tristanmcooper/courtside/plots/oura_daily_scores.png

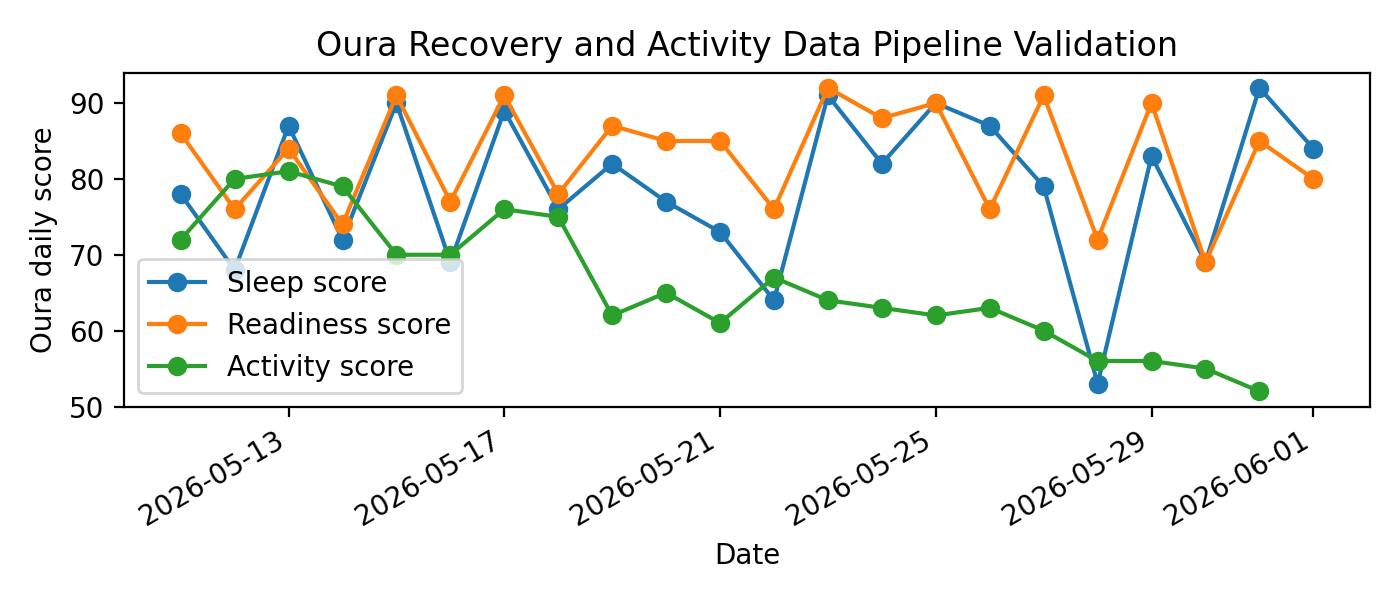
plots/oura_daily_scores.png
