tristanmcooper/courtside/updated app visuals/IMG_5117.PNG

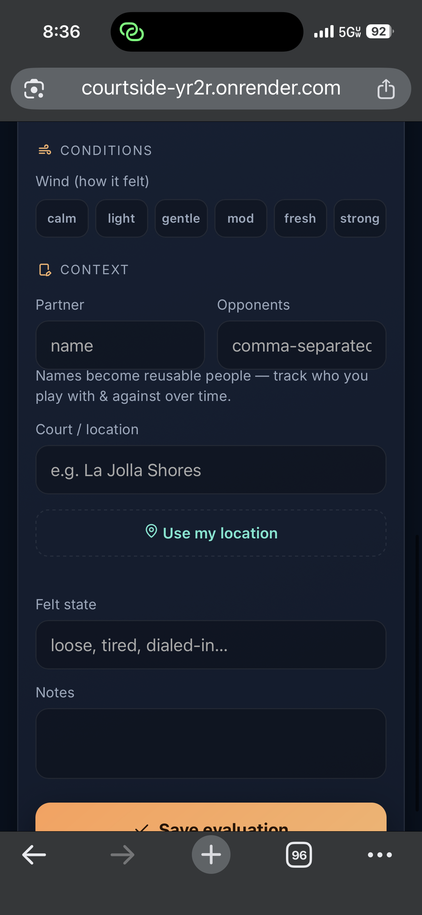
updated app visuals/IMG_5117.PNG
