tristanmcooper/courtside/updated app visuals/IMG_5119.PNG

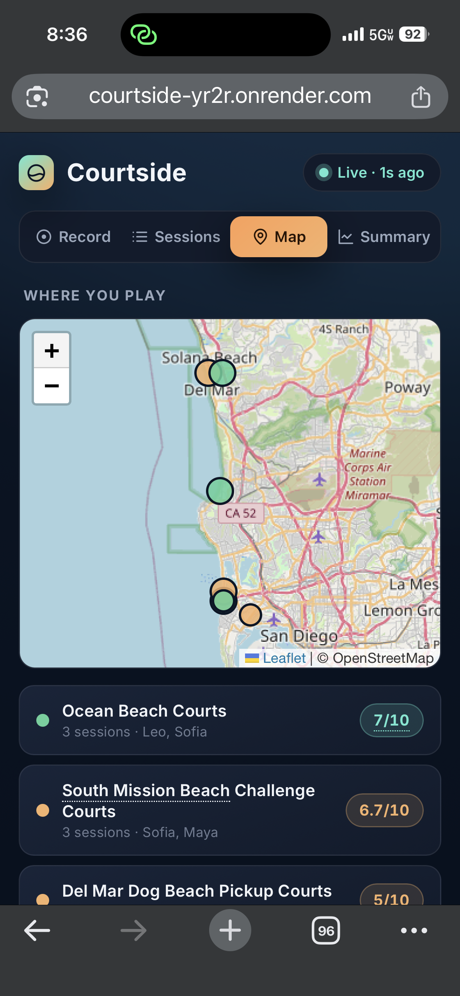
updated app visuals/IMG_5119.PNG
