tristanmcooper/courtside/updated app visuals/IMG_5123.PNG

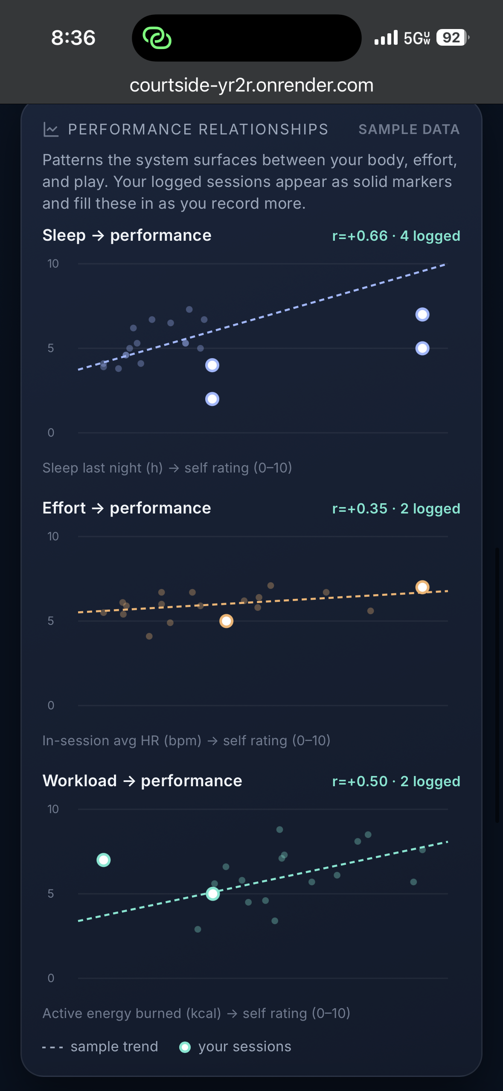
updated app visuals/IMG_5123.PNG
