tristanmcooper/courtside/updated app visuals/IMG_5125.PNG

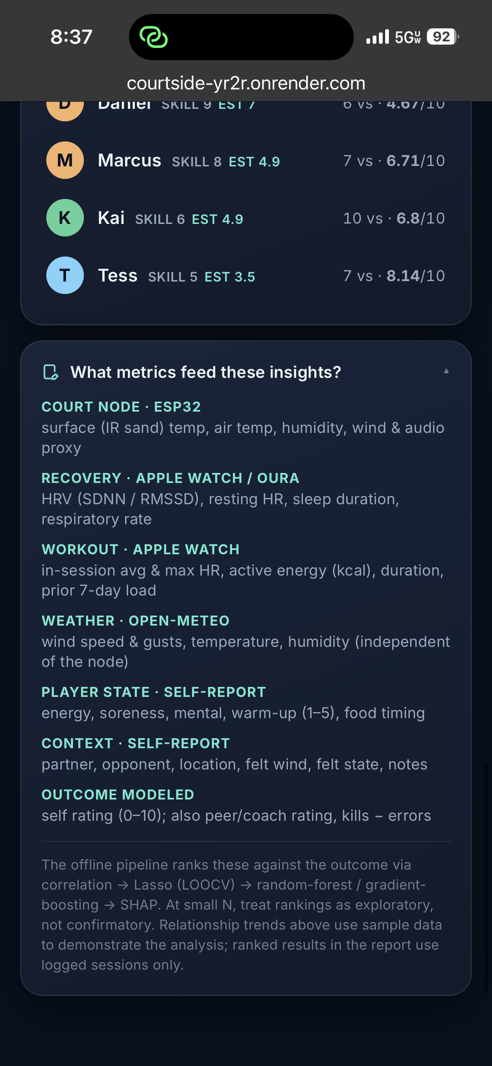
updated app visuals/IMG_5125.PNG
