tristanmcooper/courtside/visuals_for_writeup/IMG_5112.PNG

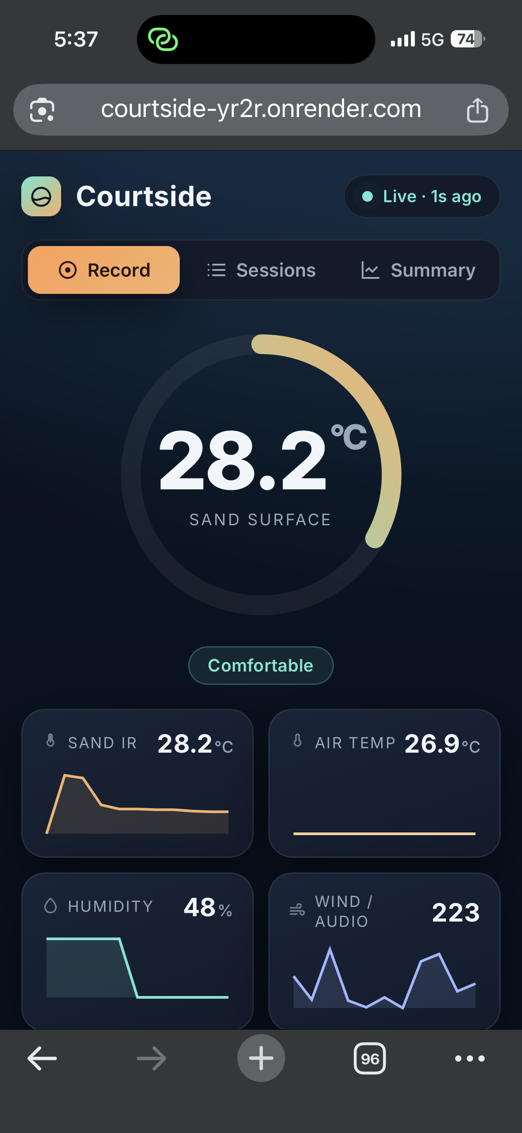
visuals_for_writeup/IMG_5112.PNG
