tristanmcooper/courtside/visuals_for_writeup/IMG_5113.PNG

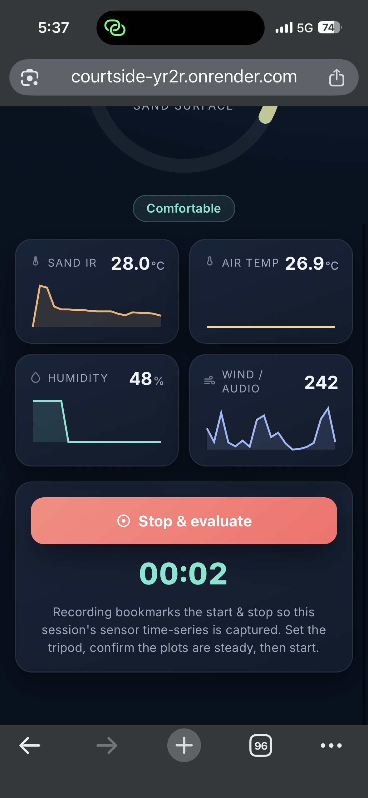
visuals_for_writeup/IMG_5113.PNG
