tristanmcooper/courtside/visuals_for_writeup/IMG_5114.PNG

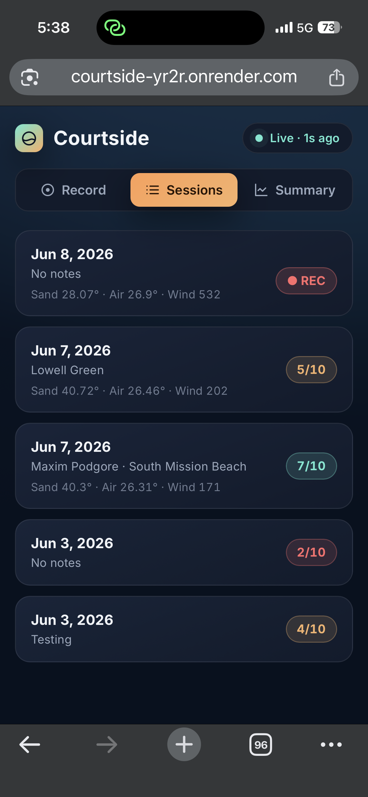
visuals_for_writeup/IMG_5114.PNG
